Hans-Beerman/NodeArgonGas/KiCad_files/NodeArgonGas/NodeArgonGas.jpg

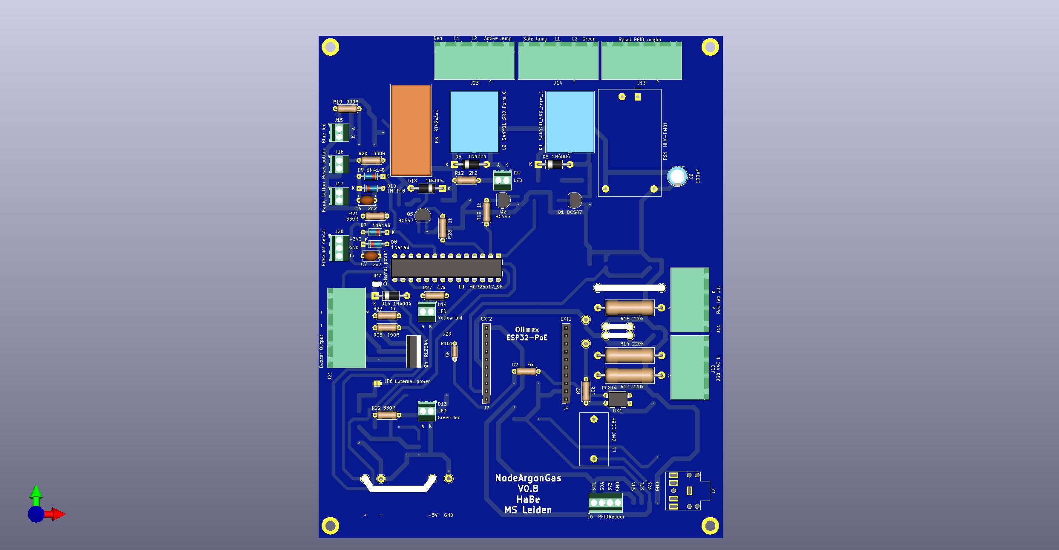
KiCad_files/NodeArgonGas/NodeArgonGas.jpg
